sulkith/BCDWristWatch/Pictures/WiringBMA.png

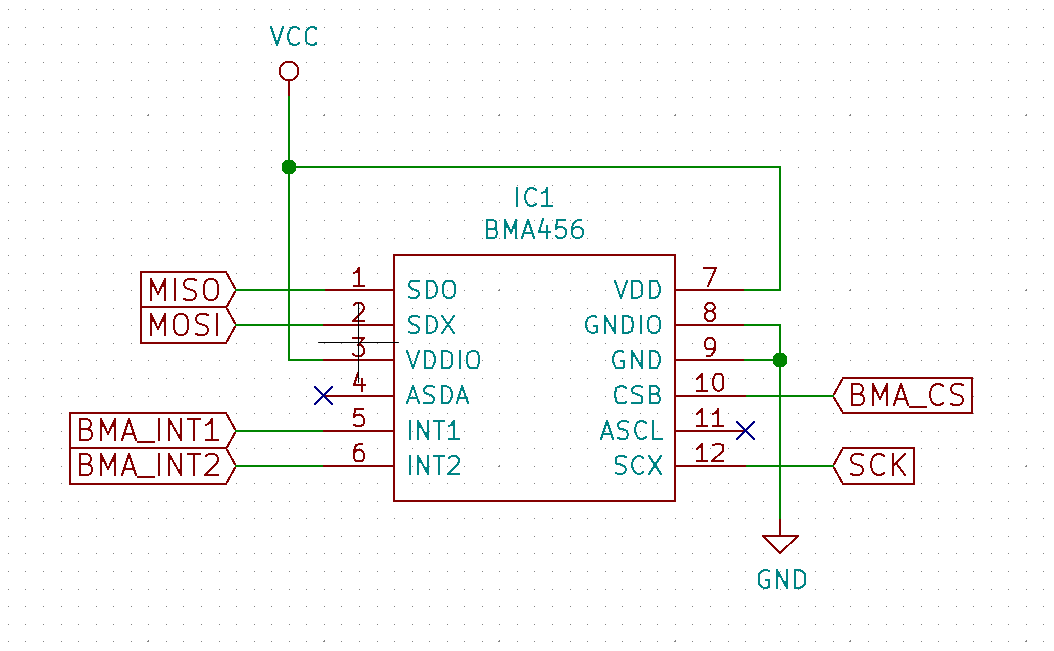
Pictures/WiringBMA.png
