sulkith/BCDWristWatch/Graphics/Date25_Dez_debouncing.pdf

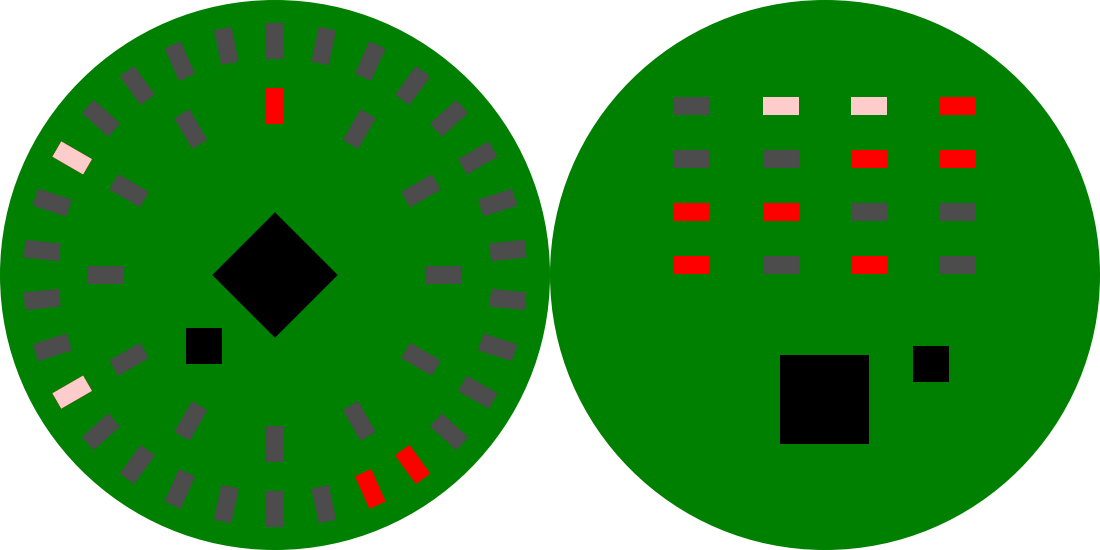
[picture p55: page 1]
