sulkith/BCDWristWatch/Graphics/Date25_Dez_SetDay.pdf

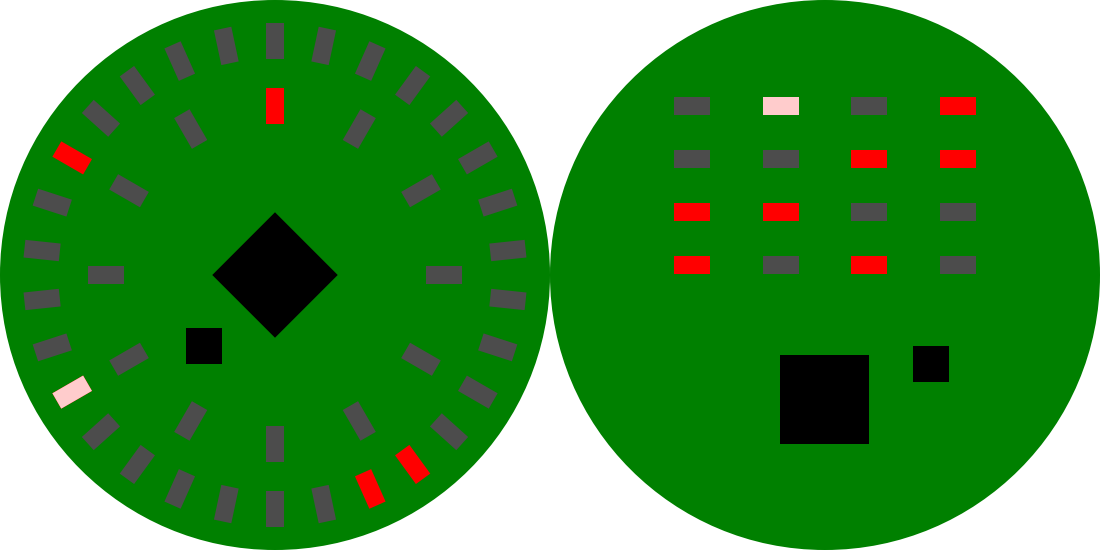
[picture p56: page 1]
