sulkith/BCDWristWatch/Graphics/Date25_Dez_SetMonth.pdf

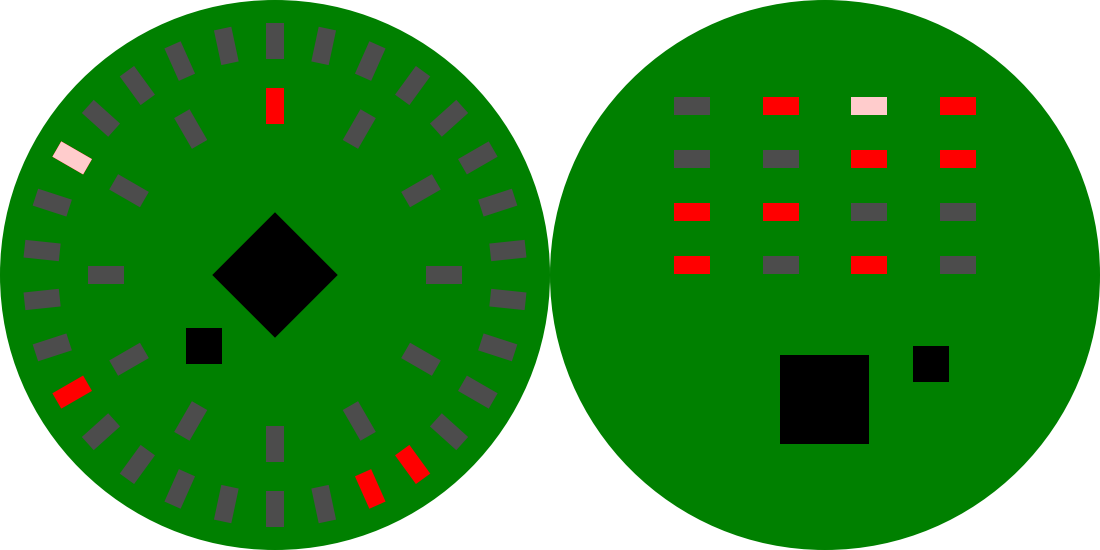
[picture p57: page 1]
