sulkith/BCDWristWatch/Graphics/Date25_Dez_SetYear21.pdf

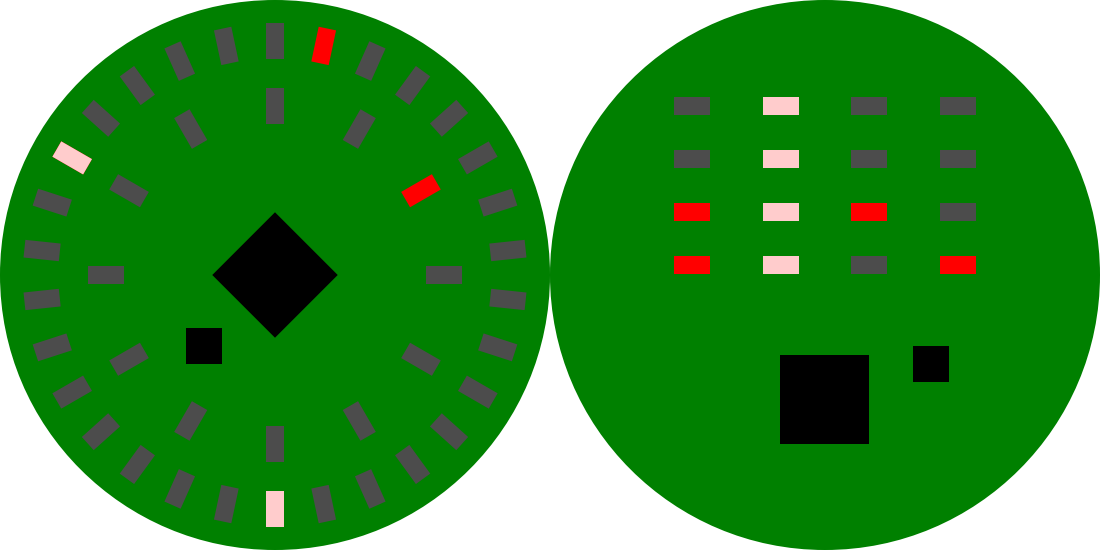
[picture p58: page 1]
