sulkith/BCDWristWatch/Graphics/ShowUBatt_2950mV.pdf

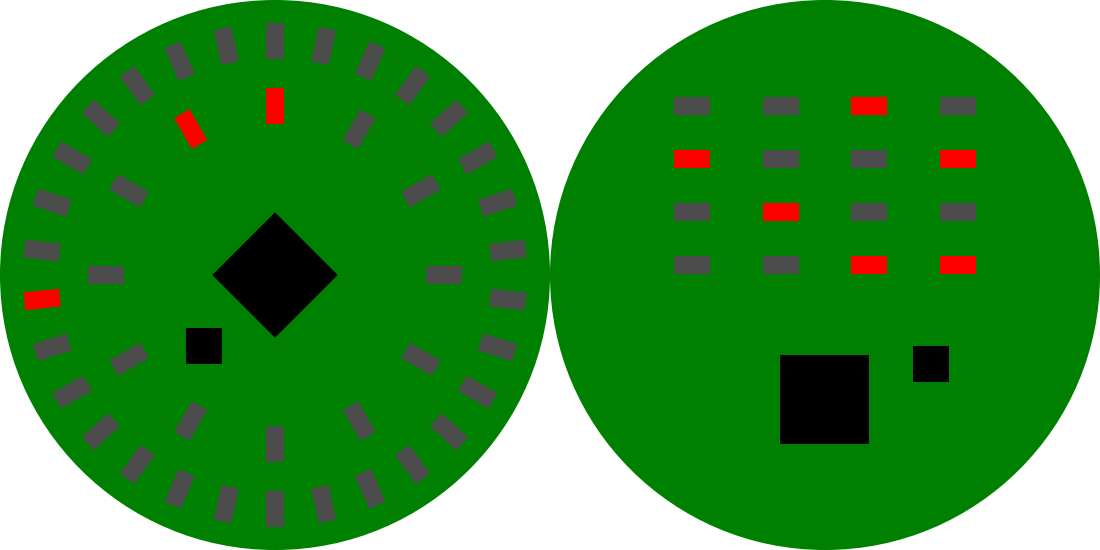
[picture p59: page 1]
