sulkith/BCDWristWatch/Graphics/Time3_15.pdf

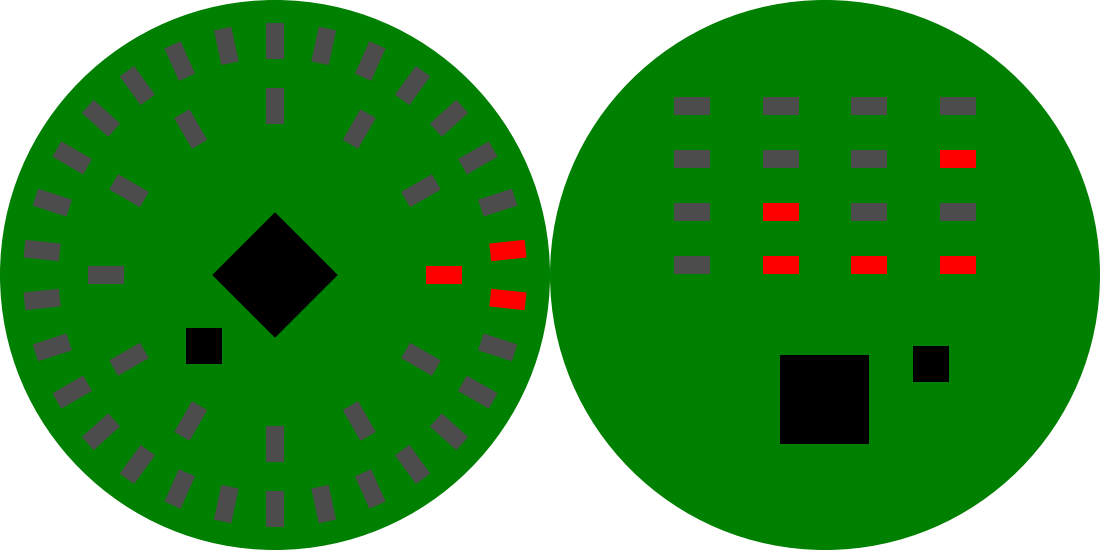
[picture p60: page 1]
