sulkith/BCDWristWatch/Graphics/Time3_15_debouncing.pdf

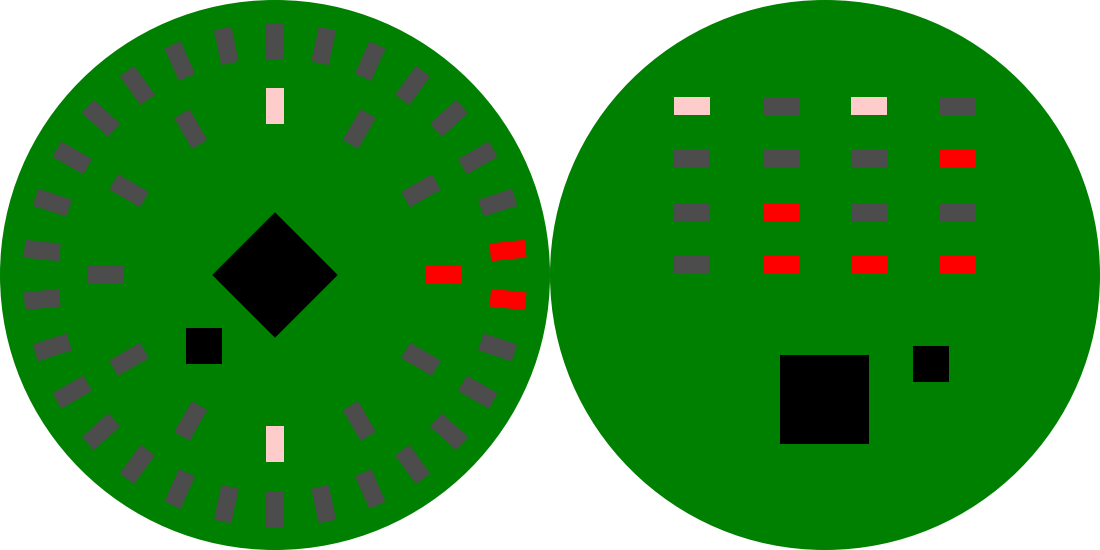
[picture p61: page 1]
