sulkith/BCDWristWatch/Graphics/Time3_15_SetHour.pdf

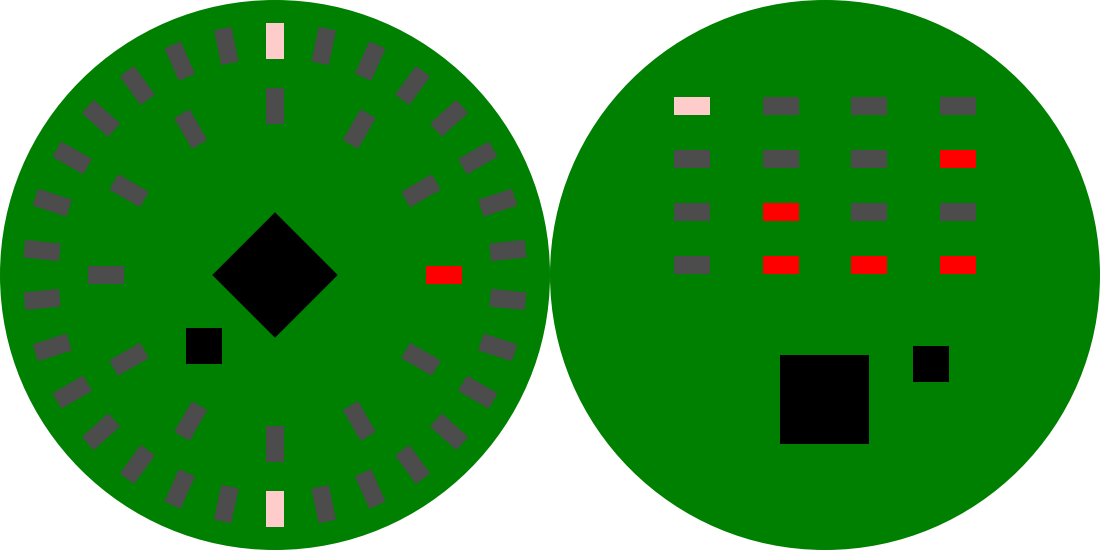
[picture p62: page 1]
