sulkith/BCDWristWatch/Graphics/Time3_15_SetMinute.pdf

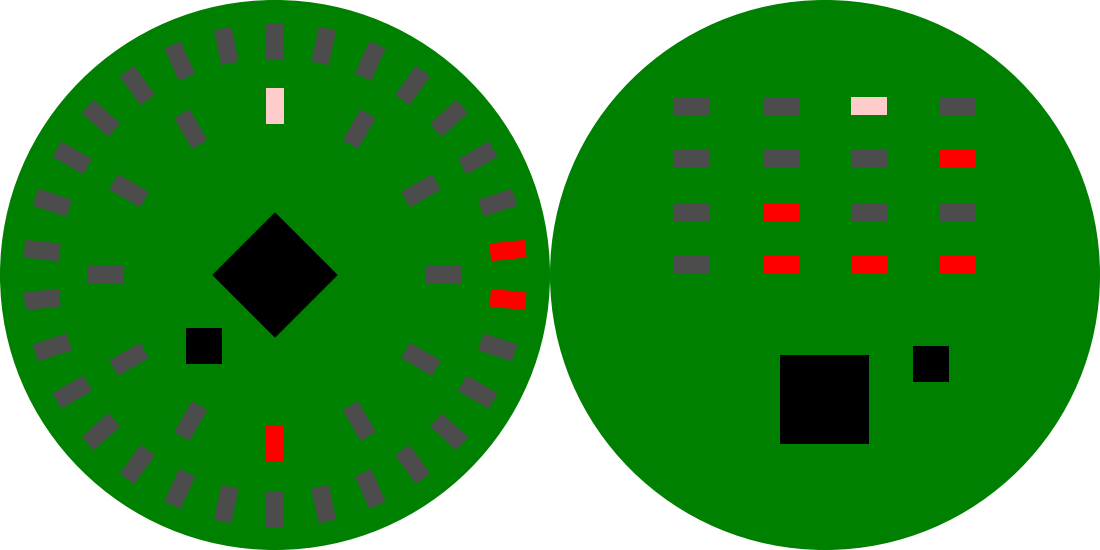
[picture p63: page 1]
