sulkith/BCDWristWatch/Software/SoftwareAtmega328P/AnalogClock_charlieArrays.h

uint8_t pbmask = 0x18;
uint8_t dbmin[] = {
0b00000000,
0b00000000,
0b00000000,
0b00000000,
0b00000000,
0b00000000,
0b00000000,
0b00000000,
0b00000000,
0b00000000,
0b00000000,
0b00000000,
0b00000000,
0b00000000,
0b00000000,
0b00000000,
0b00000000,
0b00000000,
0b00000000,
0b00100000,
0b00100000,
0b00100000,
0b00000001,
0b00000000,
0b00000001,
0b00000001,
0b00000000,
0b00000001,
0b00000000,
0b00000000,
};
uint8_t pbmin[] = {
0b00000000,
0b00000000,
0b00000000,
0b00000000,
0b00000000,
0b00000000,
0b00000000,
0b00000000,
0b00000000,
0b00000000,
0b00000000,
0b00000000,
0b00000000,
0b00000000,
0b00000000,
0b00000000,
0b00000000,
0b00000000,
0b00000000,
0b00000000,
0b00100000,
0b00000000,
0b00000000,
0b00000000,
0b00000001,
0b00000000,
0b00000000,
0b00000000,
0b00000000,
0b00000000,
};
uint8_t dcmin[] = {
0b00000000,
0b00000000,
0b00000000,
0b00000000,
0b00000000,
0b00000000,
0b00000000,
0b00100000,
0b00110000,
0b00010000,
0b00010000,
0b00011000,
0b00001000,
0b00001000,
0b00101000,
0b00000110,
0b00000011,
0b00000101,
0b00000101,
0b00000001,
0b00000100,
0b00000100,
0b00000000,
0b00000000,
0b00000000,
0b00000000,
0b00000000,
0b00000000,
0b00000000,
0b00000000,
};
uint8_t pcmin[] = {
0b00000000,
0b00000000,
0b00000000,
0b00000000,
0b00000000,
0b00000000,
0b00000000,
0b00100000,
0b00100000,
0b00000000,
0b00010000,
0b00010000,
0b00001000,
0b00000000,
0b00001000,
0b00000010,
0b00000010,
0b00000100,
0b00000001,
0b00000001,
0b00000000,
0b00000100,
0b00000000,
0b00000000,
0b00000000,
0b00000000,
0b00000000,
0b00000000,
0b00000000,
0b00000000,
};
uint8_t ddmin[] = {
0b00001100,
0b00010100,
0b00010100,
0b00000110,
0b00010010,
0b00010010,
0b00001010,
0b00000001,
0b00000000,
0b00000001,
0b00000001,
0b00000000,
0b00000001,
0b00000001,
0b00000000,
0b00000000,
0b00000000,
0b00000000,
0b00000000,
0b00000000,
0b00000000,
0b00000000,
0b10000000,
0b11000000,
0b01000000,
0b01000000,
0b01100000,
0b00100000,
0b00011000,
0b00011000,
};
uint8_t pdmin[] = {
0b00001000,
0b00010000,
0b00000100,
0b00000100,
0b00000010,
0b00010000,
0b00000010,
0b00000000,
0b00000000,
0b00000001,
0b00000000,
0b00000000,
0b00000000,
0b00000001,
0b00000000,
0b00000000,
0b00000000,
0b00000000,
0b00000000,
0b00000000,
0b00000000,
0b00000000,
0b10000000,
0b10000000,
0b00000000,
0b01000000,
0b01000000,
0b00100000,
0b00010000,
0b00001000,
};
uint8_t dbh[] = {
0b00000000,
0b00000000,
0b00000000,
0b00000000,
0b00000000,
0b00000000,
0b00000000,
0b00100000,
0b00100000,
0b00000000,
0b00000000,
0b00000000,
};
uint8_t pbh[] = {
0b00000000,
0b00000000,
0b00000000,
0b00000000,
0b00000000,
0b00000000,
0b00000000,
0b00100000,
0b00000000,
0b00000000,
0b00000000,
0b00000000,
};
uint8_t dch[] = {
0b00000000,
0b00000000,
0b00000000,
0b00110000,
0b00011000,
0b00101000,
0b00000011,
0b00000001,
0b00000010,
0b00000000,
0b00000000,
0b00000000,
};
uint8_t pch[] = {
0b00000000,
0b00000000,
0b00000000,
0b00010000,
0b00001000,
0b00100000,
0b00000001,
0b00000000,
0b00000010,
0b00000000,
0b00000000,
0b00000000,
};
uint8_t ddh[] = {
0b00001100,
0b00000110,
0b00001010,
0b00000000,
0b00000000,
0b00000000,
0b00000000,
0b00000000,
0b00000000,
0b11000000,
0b01100000,
0b10100000,
};
uint8_t pdh[] = {
0b00000100,
0b00000010,
0b00001000,
0b00000000,
0b00000000,
0b00000000,
0b00000000,
0b00000000,
0b00000000,
0b01000000,
0b00100000,
0b10000000,
};
