sulkith/BCDWristWatch/Software/SoftwareAtmega328P/GForceHAL.h

#ifndef __GFORCE_HEADER_INCLUDE__
#define __GFORCE_HEADER_INCLUDE__
#include <stdint.h>

class GForceHAL
{
public:
  virtual uint8_t getTap();
  virtual int16_t getX();
  virtual int16_t getY();
  virtual int16_t getZ();
  virtual uint32_t getSteps();
  virtual uint16_t getHistSteps(uint8_t days);
  virtual uint16_t getUBatt();
};
#endif //__GFORCE_HEADER_INCLUDE__
