sulkith/BCDWristWatch/Software/SoftwareAtmega328P/EEPM.h

#ifndef __EEPMM_HEADER_INCLUDE__
#define __EEPMM_HEADER_INCLUDE__

#include <stdint.h>
#include "SleepSubscriber.h"

typedef struct{
  uint16_t eepVers;//identifies the Version of the EEP
  uint8_t corrEveryMinute;
	uint8_t corrEveryHour;
	uint8_t corrEveryDay;
	uint8_t corrEveryMonth;
  uint16_t activatedFeatures;
  uint16_t tempOffset;
} eepBlock_t;

class EEPM: public SleepSubscriber
{
  eepBlock_t eep;
  static EEPM *instance;
public:
  EEPM();
  virtual void saveEEP(){};//Dummy Implementation
  virtual void readEEP(){};//Dummy Implementation
  virtual void iniEEP(){};//Dummy Implementation
  virtual uint8_t getCorrEveryMinute(){return eep.corrEveryMinute;}//Dummy Implementation
  virtual uint8_t getCorrEveryHour(){return eep.corrEveryHour;}//Dummy Implementation
  virtual uint8_t getCorrEveryDay(){return eep.corrEveryDay;}//Dummy Implementation
  virtual uint8_t getCorrEveryMonth(){return eep.corrEveryMonth;}//Dummy Implementation
  virtual uint16_t getActivatedFeatures(){return eep.activatedFeatures;}//Dummy Implementation
  virtual uint16_t getTempOffset(){return eep.tempOffset;}//Dummy Implementation
  virtual void setCorrEveryMinute(uint8_t t){eep.corrEveryMinute = t;}
  virtual void setCorrEveryHour(uint8_t t){eep.corrEveryHour = t;}
  virtual void setCorrEveryDay(uint8_t t){eep.corrEveryDay = t;}
  virtual void setCorrEveryMonth(uint8_t t){eep.corrEveryMonth = t;}
  virtual void setActivatedFeatures(uint16_t t){eep.activatedFeatures = t;}
  virtual void setTempOffset(uint16_t t){eep.tempOffset = t;}
  virtual void executeSleepSubscription(){saveEEP();};//Dummy Implementation
  static void setInstance(EEPM *inst){instance = inst;}
  static EEPM *getInstance(){return instance;}
  EEPM(EEPM const&)               = delete;
  void operator=(EEPM const&)     = delete;
};
#endif //__EEPMM_HEADER_INCLUDE__
