sulkith/BCDWristWatch/Software/SoftwareAtmega328P/SleepSubscriber.h

#ifndef __SLEEPSUBSCRIBER_HEADER_INCLUDE__
#define __SLEEPSUBSCRIBER_HEADER_INCLUDE__
class SleepSubscriber
{
  public:
    virtual void executeSleepSubscription()=0;
};
#endif //__SLEEPSUBSCRIBER_HEADER_INCLUDE__
