sulkith/BCDWristWatch/Software/SoftwareAtmega328P/TwoButtonUI.h

#ifndef ___TWOBUTTONUI_HEADER_INCLUDE__
#define ___TWOBUTTONUI_HEADER_INCLUDE__
#include "UserInterface.h"
#include "TwoButtonHAL.h"
#include "HAL.h"
#include "Debouncer.h"
#include "DisplayManager.h"
#include "DisplayRequest.h"
#include "SleepSubscriber.h"

class TwoButtonUI: public UserInterface, public SleepSubscriber
{
  Debouncer<uint8_t> *rightButton;
  Debouncer<uint8_t> *leftButton;
  HAL *mHal;
  DisplayManager *DisplMan;
  DisplayRequestType UIstate = FadeIn;
  bool inputEnabled = false;
  void stateTransition();
  void stateDisplayReuest();
public:
  virtual void cyclic();
  virtual void init();
  TwoButtonUI(HAL *hwhal,TwoButtonHAL *tbh, DisplayManager *dm):
  rightButton(tbh->getRightButtonDeb()), leftButton(tbh->getLeftButtonDeb()),
  mHal(hwhal), DisplMan(dm){};
  TwoButtonUI():rightButton(NULL), leftButton(NULL),
  mHal(NULL), DisplMan(NULL){};
  virtual void executeSleepSubscription();
};

#endif //___TWOBUTTONUI_HEADER_INCLUDE__
